SP6GK/LPF_Board_HF-6m_Forte600/Results/4030m2.png

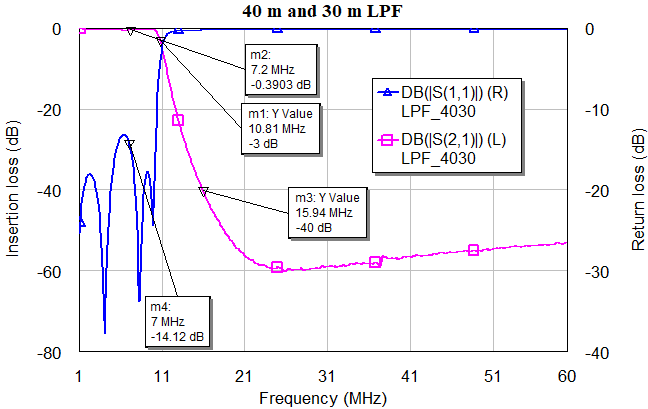
Results/4030m2.png
