SP6GK/LPF_Board_HF-6m_Forte600/Results/AWR_6m2.png

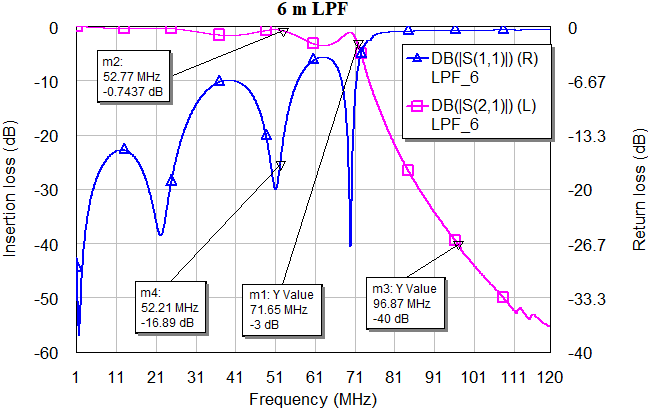
Results/AWR_6m2.png
