SP6GK/LPF_Board_HF-6m_Forte600/Results/AWR_80m2.png

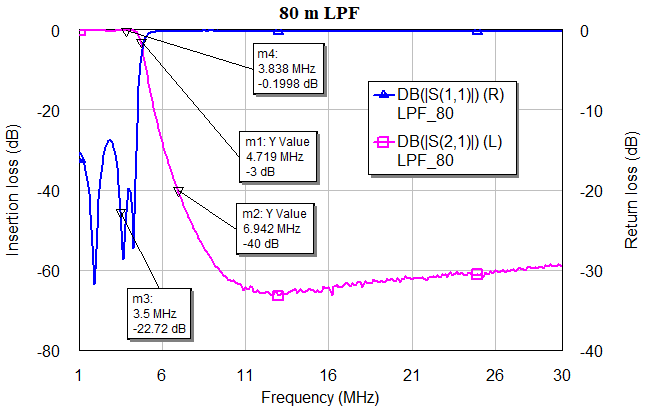
Results/AWR_80m2.png
