SP6GK/LPF_Board_HF-6m_Forte600/Results/AWR_2017m2.png

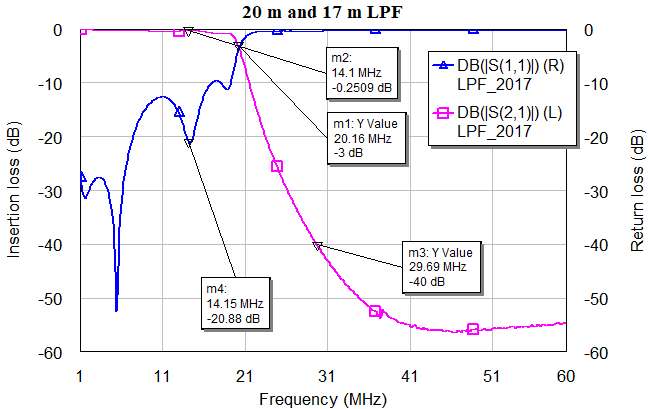
Results/AWR_2017m2.png
