SP6GK/LPF_Board_HF-6m_Forte600/LPF.asc

C1: cap; 1500p
C2: cap; 1500p
C3: cap; 2800p
C4: cap; 360p
C5: cap; 360p
C6: cap; 688p
C7: cap; 223p
C8: cap; 3n
C9: cap; 3n
C10: cap; 223p
C11: cap; 426p
C12: cap; 650p
C13: cap; 650p
C14: cap; 1200p
C15: cap; 5.7n
C16: cap; 71p
C17: cap; 71p
C18: cap; 123p
C19: cap; 71p
C20: cap; 71p
C21: cap; 127p
C22: cap; 127p
C23: cap; 123p
C24: cap; 123p
C25: cap; 218p
C26: cap; 218p
C27: cap; 203p
C28: cap; 788p
C29: cap; 788p
C30: cap; 1500p
C31: cap; 203p
C32: cap; 360p
C33: cap; 360p
C34: cap; 357p
C35: cap; 357p
C36: cap; 635p
C37: cap; 635p
C38: cap; 834p
C39: cap; 834p
C40: cap; 1480p
C41: cap; 1480p
C42: cap; 1633p
C43: cap; 1633p
C44: cap; 2900p
C45: cap; 2900p
C46: cap; 481p
C47: cap; 481p
C48: cap; 855p
C49: cap; 855p
C50: cap; 4.67n
C51: cap; 4.67n
C52: cap; 4.4n
C53: cap; 80p
C54: cap; 80p
C55: cap; 173p
C56: cap; 173p
C57: cap; 80p
C58: cap; 80p
C59: cap; 173p
C60: cap; 173p
C61: cap; 80p
C62: cap; 80p
C63: cap; 120p
C64: cap; 120p
L1: ind; 0.789µ
L2: ind; 1.51µ
L3: ind; 0.36µ
L4: ind; 0.36µ
L5: ind; 0.22µ
L6: ind; 1.51µ
L7: ind; 0.22µ
L8: ind; 0.21µ
L9: ind; 0.21µ
L10: ind; 0.789µ
L11: ind; 0.65µ
L12: ind; 0.65µ
L13: ind; 0.22µ
L14: ind; 3µ; Rser=0.08
L15: ind; 3µ; Rser=0.08
L16: ind; 0.24µ
L17: ind; 0.22µ
L18: ind; 0.371µ
L19: ind; 0.41µ
L20: ind; 0.371µ
L21: ind; 0.612µ
L22: ind; 0.676µ
L23: ind; 0.612µ
L24: ind; 1µ
L25: ind; 1.2µ
L26: ind; 1µ
L27: ind; 2.51µ
L28: ind; 2.78µ
L29: ind; 2.51µ
L30: ind; 4.923µ; Rser=0.08
L31: ind; 5.44µ; Rser=0.08
L32: ind; 4.923µ; Rser=0.08
L33: ind; 1.452µ
L34: ind; 1.6µ
L35: ind; 1.452µ
L36: ind; 4.7µ; Rser=0.08
L37: ind; 4.7µ; Rser=0.08
L38: ind; 0.28µ
L39: ind; 0.37µ
L40: ind; 0.28µ
L41: ind; 0.37µ
L42: ind; 0.47µ
L43: ind; 0.37µ
L44: ind; 0.17µ
L45: ind; 0.39µ
L46: ind; 0.16µ
R1: res; 50
R2: res; 50
R3: res; 50
R4: res; 50
R5: res; 50
R6: res; 50
R7: res; 50
R8: res; 50
R9: res; 50
R10: res; 50
R11: res; 50
R12: res; 50
R13: res; 50
R14: res; 50
R15: res; 50
R16: res; 50
R17: res; 50
R18: res; 50
V1: voltage; ""; AC 1; Rser=50
V2: voltage; ""; AC 1; Rser=50
V3: voltage; ""; AC 1; Rser=50
V4: voltage; ""; AC 1; Rser=50
V5: voltage; ""; AC 1; Rser=50
V6: voltage; ""; AC 1; Rser=50
V7: voltage; ""; AC 1; Rser=50
V8: voltage; ""; AC 1; Rser=50
V9: voltage; ""; AC 1; Rser=50
V10: voltage; ""; AC 1; Rser=50
V11: voltage; ""; AC 1; Rser=50
V12: voltage; ""; AC 1; Rser=50
V13: voltage; ""; AC 1; Rser=50
V14: voltage; ""; AC 1; Rser=50
V15: voltage; ""; AC 1; Rser=50
V16: voltage; ""; AC 1; Rser=50
V17: voltage; ""; AC 1; Rser=50
V18: voltage; ""; AC 1; Rser=50
Named nets: 0, SP_40/30m, SP_80m, SP160m, SP_40m, cheby5_20/17m, SP_15/10m, SP_6m, cheby7_6m, cheby7_15/10m, cheby7_20/17m, cheby7_40/30m, cheby7_80m, cheby7_160m, cheby7_40, SP160mediumm, cheby7_15/10m_Current, cheby7_15/10m_new, 26pql
.ac dec 1k 1meg 120meg
Spherical 40m + 30m, ~20dB
Dedicated 80m
Dedicated 160m
20/17
Dedicated 40m ~30dB
Dedicated 15-10m
Dedicated 6m
10-15 cheby 0.1dB 7
cheby is even better than spherical and L is higher
This and above can be very likely airwound
Chebyschev 40m + 30m, ~24dB
Cheby is better again but check if inductances here are easy, if not use SP
Just use Spherical, Cheby requires more inductance so three large toroids - not enough space on PCB and SP gives more than 30 dB anyway
Dedicated 160m
0.37u - 8 turns 0.47u -9 turns t94-10
0.37u - 8 turns is precise, 0.47 is not make 0.47u air wound?
current+new caps
